CatoLynx/LCD-FIA/Hardware/FIAControl/Contrast Power Stage.asc

I1: current; PULSE(100m -100m 0 10µ 10µ 1m 2m)
Q1: npn
Q2: pnp
R1: res; 56k
R2: res; 91k
R3: res; 1k
U1: UniversalOpamp2
V1: voltage; 12
V2: voltage; PULSE(0 3.3 0 1 0 1 1)
Named nets: 0, Out
.tran 1s
