CatoLynx/LCD-FIA/STM32/Aditech LCD Test/Src/main.c

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

/* Includes ------------------------------------------------------------------*/
#include "main.h"
#include "dma.h"
#include "gpio.h"
#include "spi.h"
#include "tim.h"
#include "usb_device.h"

/* USER CODE BEGIN Includes */
#include "aditech.h"
#include "communication.h"
#include "globals.h"
#include "usbd_cdc_if.h"
/* USER CODE END Includes */


/* USER CODE BEGIN PV */
uint8_t lcdData[LCD_BUF_SIZE];
uint8_t currentRAM = RAM1;
/* USER CODE END PV */

void SystemClock_Config(void);
/* USER CODE BEGIN 0 */
void GPIO_USB_DP_Init(void) {
    GPIO_InitTypeDef GPIO_InitStruct = {0};

    /* GPIO Ports Clock Enable */
    __HAL_RCC_GPIOD_CLK_ENABLE();
    __HAL_RCC_GPIOA_CLK_ENABLE();

    /*Configure GPIO pin Output Level */
    HAL_GPIO_WritePin(GPIOA, GPIO_PIN_12, GPIO_PIN_RESET);

    /*Configure GPIO pin : PA1 */
    GPIO_InitStruct.Pin = GPIO_PIN_12;
    GPIO_InitStruct.Mode = GPIO_MODE_OUTPUT_PP;
    GPIO_InitStruct.Pull = GPIO_NOPULL;
    GPIO_InitStruct.Speed = GPIO_SPEED_FREQ_LOW;
    HAL_GPIO_Init(GPIOA, &GPIO_InitStruct);
}
/* USER CODE END 0 */

/**
 * @brief  The application entry point.
 * @retval int
 */
int main(void) {
    /* MCU Configuration--------------------------------------------------------*/

    /* Reset of all peripherals, Initializes the Flash interface and the Systick. */
    HAL_Init();

    /* Configure the system clock */
    SystemClock_Config();

    /* USER CODE BEGIN SysInit */
    // Force USB re-enumerate
    GPIO_USB_DP_Init();
    HAL_Delay(10);
    /* USER CODE END SysInit */

    /* Initialize all configured peripherals */
    MX_GPIO_Init();
    MX_DMA_Init();
    MX_SPI1_Init();
    MX_TIM2_Init();
    MX_USB_DEVICE_Init();
    MX_TIM3_Init();
    MX_SPI2_Init();
    /* USER CODE BEGIN 2 */
    HAL_TIM_Base_Start(&DELAY_US_TIMER);
    HAL_TIM_Base_Start(&LCD_FRAME_TIMER);
    HAL_TIM_PWM_Start(&LCD_FRAME_TIMER, LCD_FRAME_TIMER_CHANNEL);
    memset(lcdData, 0x37, LCD_BUF_SIZE);
    /* USER CODE END 2 */

    /* Infinite loop */
    /* USER CODE BEGIN WHILE */
    while (1) {
        /* USER CODE END WHILE */

        /* USER CODE BEGIN 3 */
        if (!isTransmitActive()) {
            //convertBitmap(lcdData, bitmapBuffer, NUM_HALF_PANELS, currentRAM);
            transmitBitmap(lcdData, NUM_HALF_PANELS);
            if (currentRAM == RAM1) {
                currentRAM = RAM2;
            } else {
                currentRAM = RAM1;
            }
        }
        HAL_Delay(1000);
    }
    /* USER CODE END 3 */
}

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
