CatoLynx/LCD-FIA/STM32/Aditech LCD Test/Inc/globals.h

#define LCD_SPI1 hspi1
#define LCD_SPI2 hspi2
#define LCD_FRAME_TIMER htim2
#define LCD_FRAME_TIMER_CHANNEL TIM_CHANNEL_1
#define DELAY_US_TIMER htim3
#define LCD_LATCH GPIOA, GPIO_PIN_1
